linzi0928/STM32_VFD_CLOCK_DS3231/STM32_Keil_Project/HARDWARE/DS3231/gpio.c

#include"gpio.h"

void GPIO_Config(void)
{
	GPIO_InitTypeDef GPIO_InitStructure;
	
	RCC_APB2PeriphClockCmd(RCC_APB2Periph_GPIOB,ENABLE);
	
	GPIO_InitStructure.GPIO_Pin=GPIO_Pin_11|GPIO_Pin_10;
	GPIO_InitStructure.GPIO_Mode=GPIO_Mode_Out_PP;
	GPIO_InitStructure.GPIO_Speed=GPIO_Speed_50MHz;
	
	
	
	GPIO_Init(GPIOB,&GPIO_InitStructure);	
}

void IIC_SDA_OUT(void)
{
	GPIO_InitTypeDef GPIO_InitStructure;
	
	RCC_APB2PeriphClockCmd(RCC_APB2Periph_GPIOB,ENABLE);
	
	GPIO_InitStructure.GPIO_Pin=GPIO_Pin_11;
	GPIO_InitStructure.GPIO_Mode=GPIO_Mode_Out_PP;
	GPIO_InitStructure.GPIO_Speed=GPIO_Speed_50MHz;

	GPIO_Init(GPIOB,&GPIO_InitStructure);
}

void IIC_SDA_IN(void)
{
	GPIO_InitTypeDef GPIO_InitStructure;
	
	RCC_APB2PeriphClockCmd(RCC_APB2Periph_GPIOB,ENABLE);
	
	GPIO_InitStructure.GPIO_Pin=GPIO_Pin_11;
	GPIO_InitStructure.GPIO_Mode=GPIO_Mode_IPU;

	GPIO_Init(GPIOB,&GPIO_InitStructure);
}
